gonogo312/NewEyes/Snapshots/Examples/troley.png

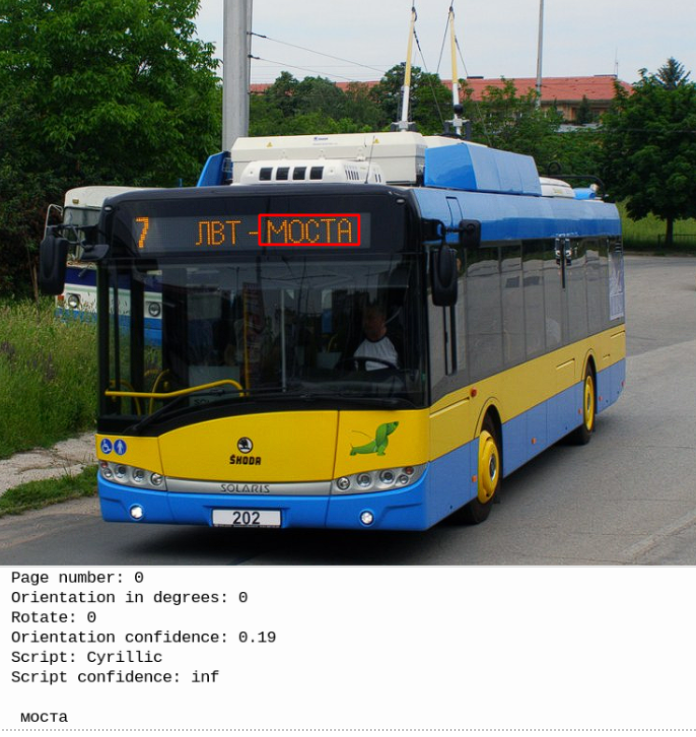
Snapshots/Examples/troley.png
