gonogo312/NewEyes/Snapshots/SampleData/other_datasets/book_image_samples/howireachedhometilted.jpg

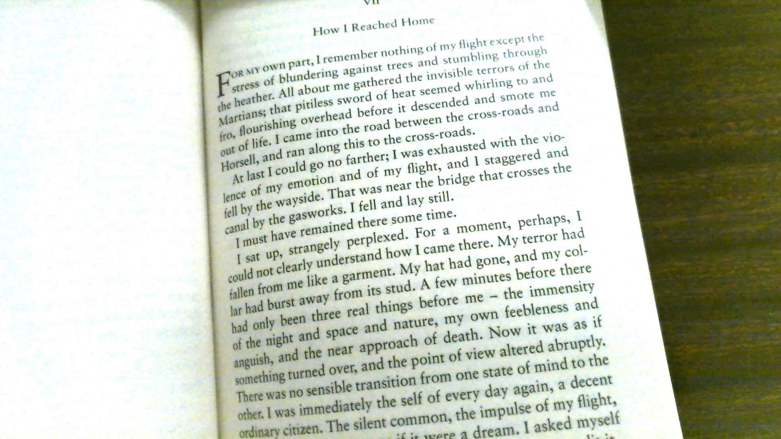
Snapshots/SampleData/other_datasets/book_image_samples/howireachedhometilted.jpg
