gonogo312/NewEyes/Snapshots/SampleData/other_datasets/street_image_samples/ford.webp

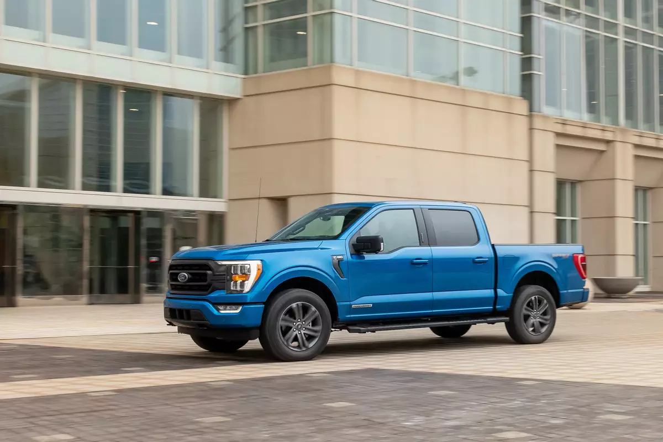
Snapshots/SampleData/other_datasets/street_image_samples/ford.webp
