gonogo312/NewEyes/Snapshots/SampleData/other_datasets/street_image_samples/goce_delchev.jpg

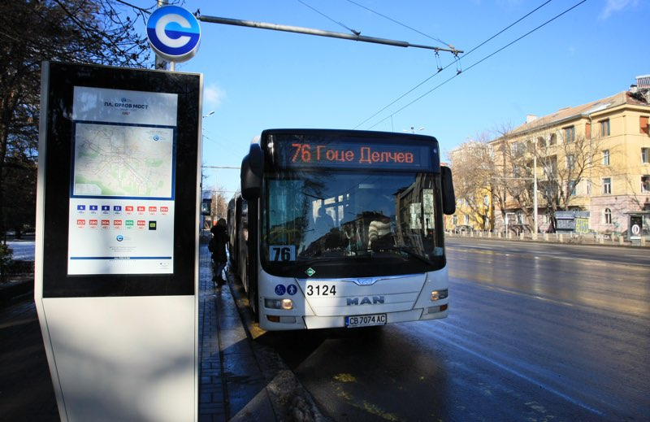
Snapshots/SampleData/other_datasets/street_image_samples/goce_delchev.jpg
