gonogo312/NewEyes/Snapshots/SampleData/other_datasets/street_image_samples/kliment_ohridski.jpg

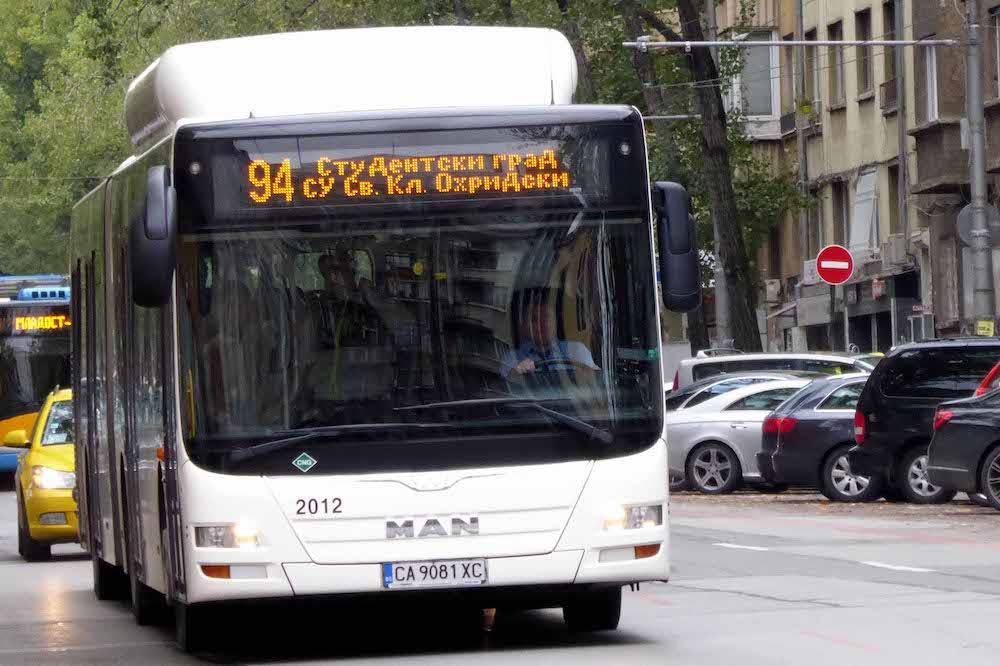
Snapshots/SampleData/other_datasets/street_image_samples/kliment_ohridski.jpg
