gonogo312/NewEyes/Snapshots/SampleData/other_datasets/street_image_samples/shadwell.png

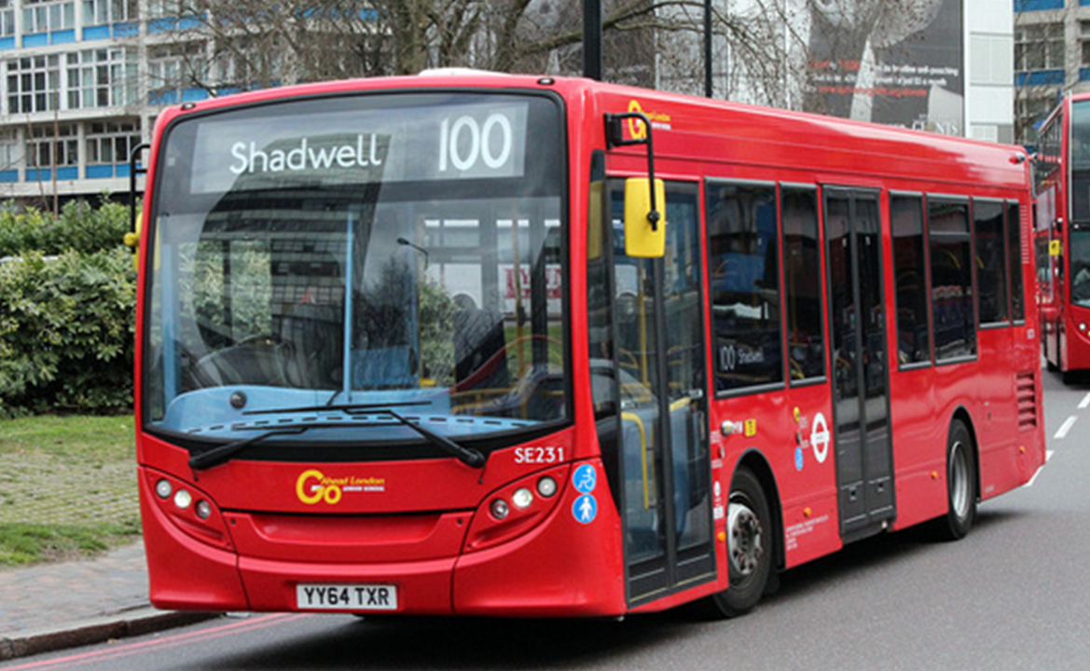
Snapshots/SampleData/other_datasets/street_image_samples/shadwell.png
