gonogo312/NewEyes/Snapshots/SampleData/other_datasets/street_image_samples/stopsign.png

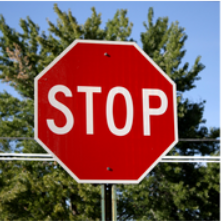
Snapshots/SampleData/other_datasets/street_image_samples/stopsign.png
