gonogo312/NewEyes/Snapshots/SampleData/other_datasets/street_image_samples/woodlands.jpg

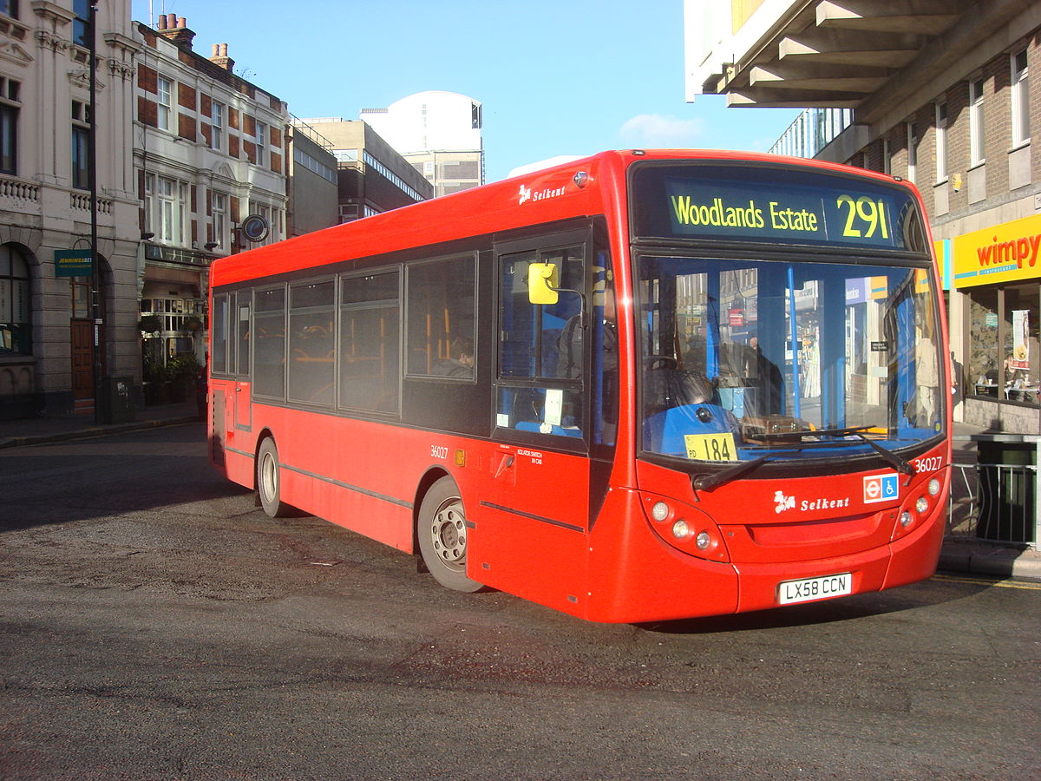
Snapshots/SampleData/other_datasets/street_image_samples/woodlands.jpg
