gonogo312/NewEyes/Snapshots/Videos/image00003.jpeg

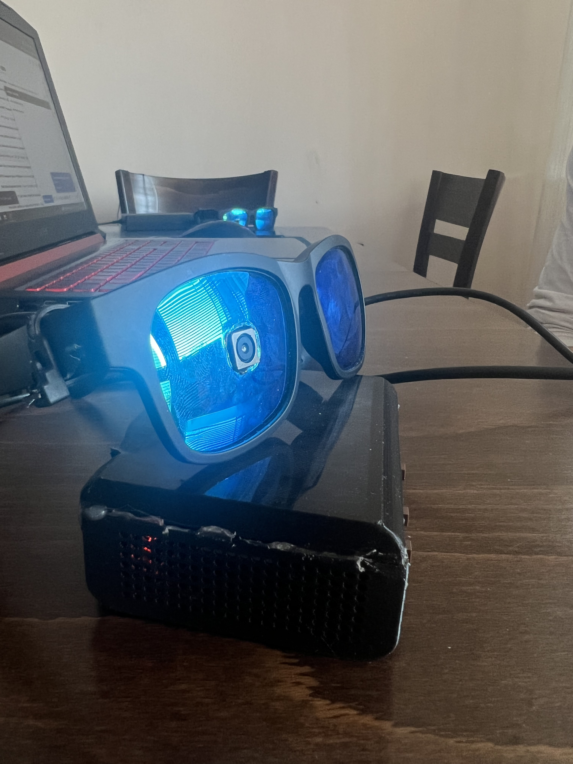
Snapshots/Videos/image00003.jpeg
