gonogo312/NewEyes/Snapshots/Videos/image00002.jpeg

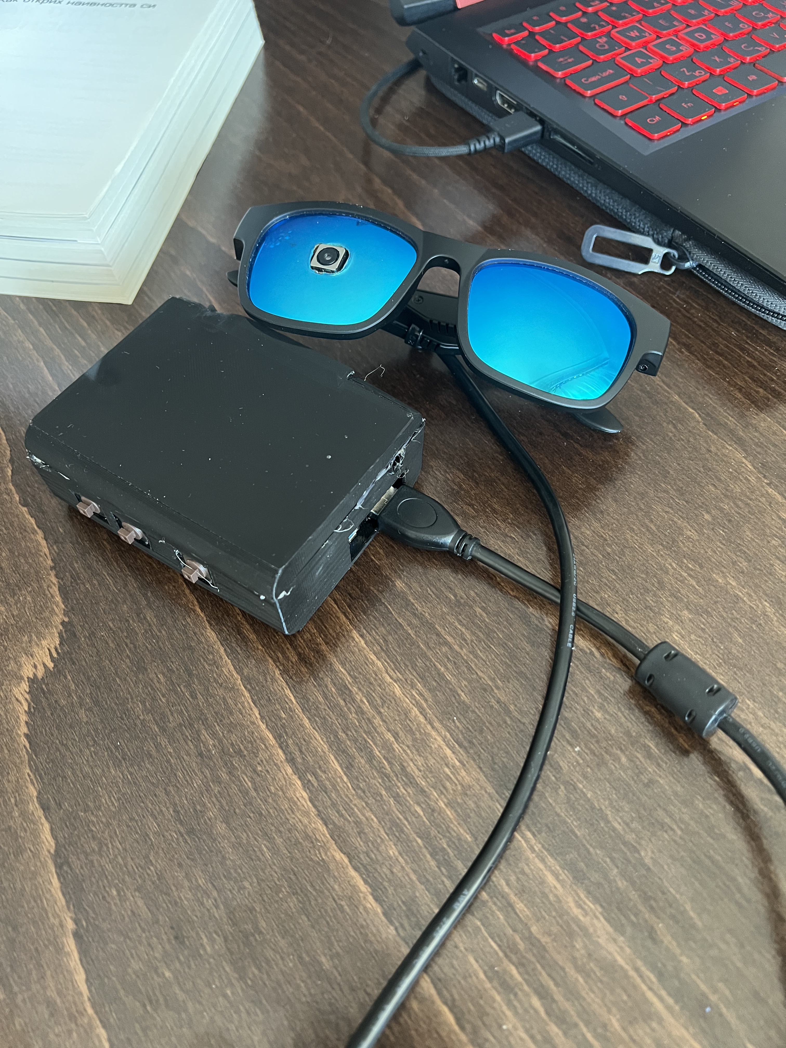
Snapshots/Videos/image00002.jpeg
